mgineer85/sFeeder/parametric_feeder_desc2.png

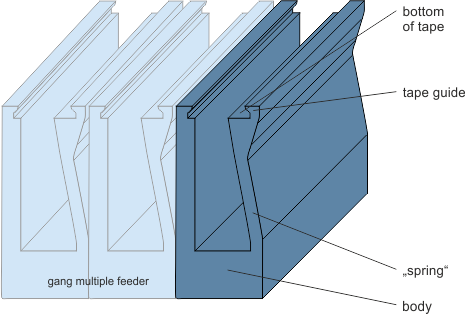
parametric_feeder_desc2.png
