mgineer85/sFeeder/parametric_feeder_desc_raw.png

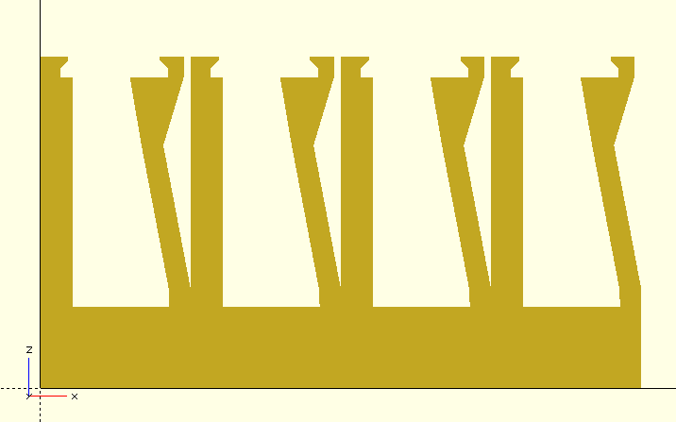
parametric_feeder_desc_raw.png
