mgineer85/sFeeder/sFeederOpenSCAD_edited.png

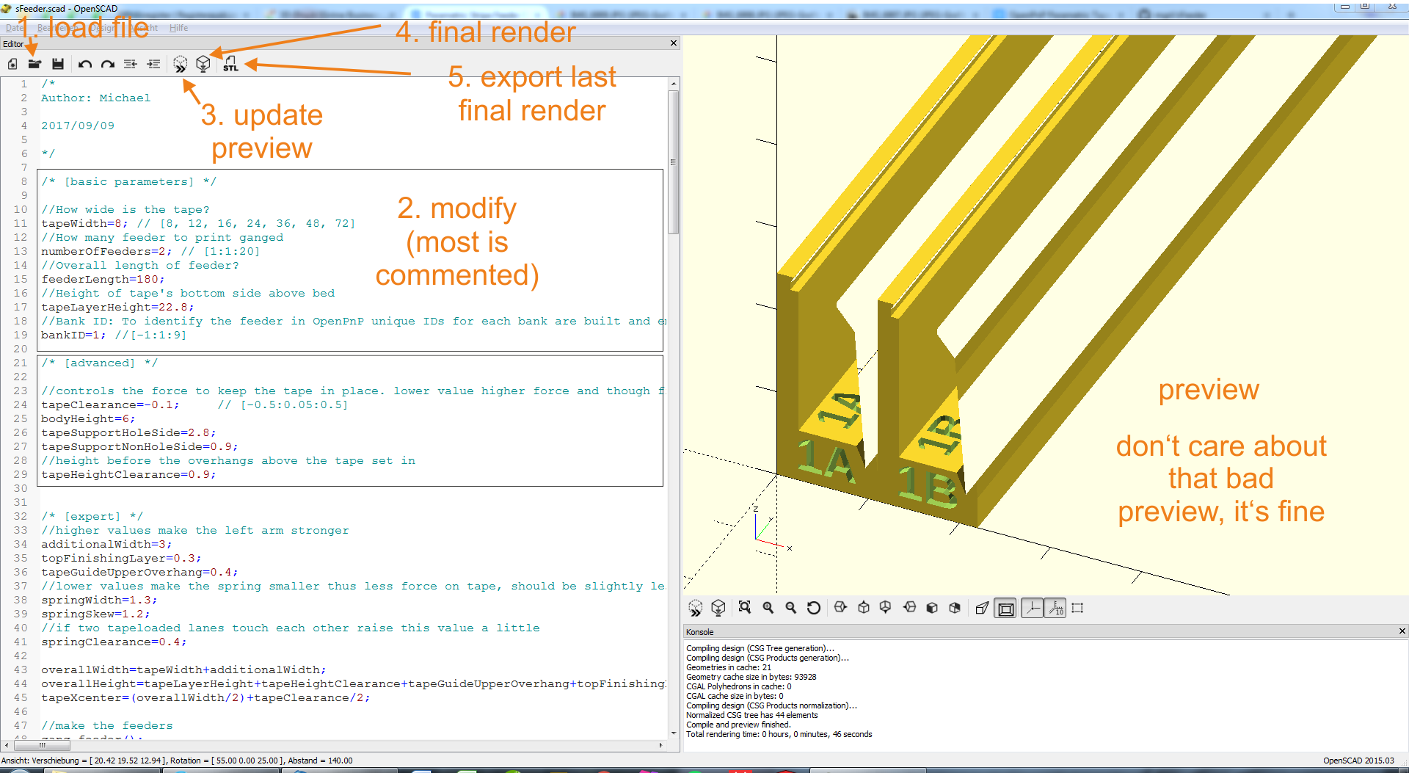
sFeederOpenSCAD_edited.png
